Jaffe-/NESizer2/src/io/ringbuffer.c

#include <stdint.h>
#include "ringbuffer.h"
#include "ui/ui.h"

#define ERROR_RINGBUF_WRITE_OFLOW (1 << 0)
#define ERROR_RINGBUF_READ_UFLOW (1 << 1)

uint8_t ring_buffer_read(struct ring_buffer *buffer)
{
    uint8_t value = buffer->data[buffer->read_pos];

    /* Underflow */
    if (buffer->read_pos == buffer->write_pos)
        error_set(ERROR_RINGBUF_READ_UFLOW);

    if (++buffer->read_pos == SIZE)
        buffer->read_pos = 0;

    return value;
}

void ring_buffer_write(struct ring_buffer *buffer, uint8_t value)
{
    buffer->data[buffer->write_pos] = value;

    if (++buffer->write_pos == SIZE)
        buffer->write_pos = 0;

    /* Overflow */
    if (buffer->write_pos == buffer->read_pos)
        error_set(ERROR_RINGBUF_WRITE_OFLOW);
}

uint8_t ring_buffer_bytes_remaining(const struct ring_buffer *buffer)
{
    if (buffer->write_pos >= buffer->read_pos)
        return buffer->write_pos - buffer->read_pos;
    else
        return SIZE - (buffer->read_pos - buffer->write_pos);
}

uint8_t ring_buffer_peek(struct ring_buffer *buffer)
{
    return buffer->data[buffer->read_pos];
}
